jangleboom/RTKRover/src/CasterSecrets.h

/** A place for your caster credentials.
 * 
 * Except of the (empty) kCasterUserPw[], this will be not used if 
 * you use the web form of the RTKRoverManager for credential input.
 * 
 * Check if your base station is online: http://www.rtk2go.com:2101/SNIP::STATUS#uptime
 */ 

#ifndef CASTER_SECRETS_H
#define CASTER_SECRETS_H

const char kCasterHost[] = "rtk2go.com"; 
const char kCasterPort[] = "2101";
const char kMountPoint[] = "YOUR_MOUNT_POINT";
const char kCasterUser[] = "YOUR_USER_EMAIL";           // User must provide their own email address to use RTK2Go
const char kCasterUserPw[] = "";                        // Not neccecary, more info: rtk2go.com

// Device name 
const char kDeviceName[] = "roverli";                   // E. g. 

#endif /*** CASTER_SECRETS_H ***/
